tebl/C64-Pi1541-II/gallery/2020-09-29 00.47.54.jpg

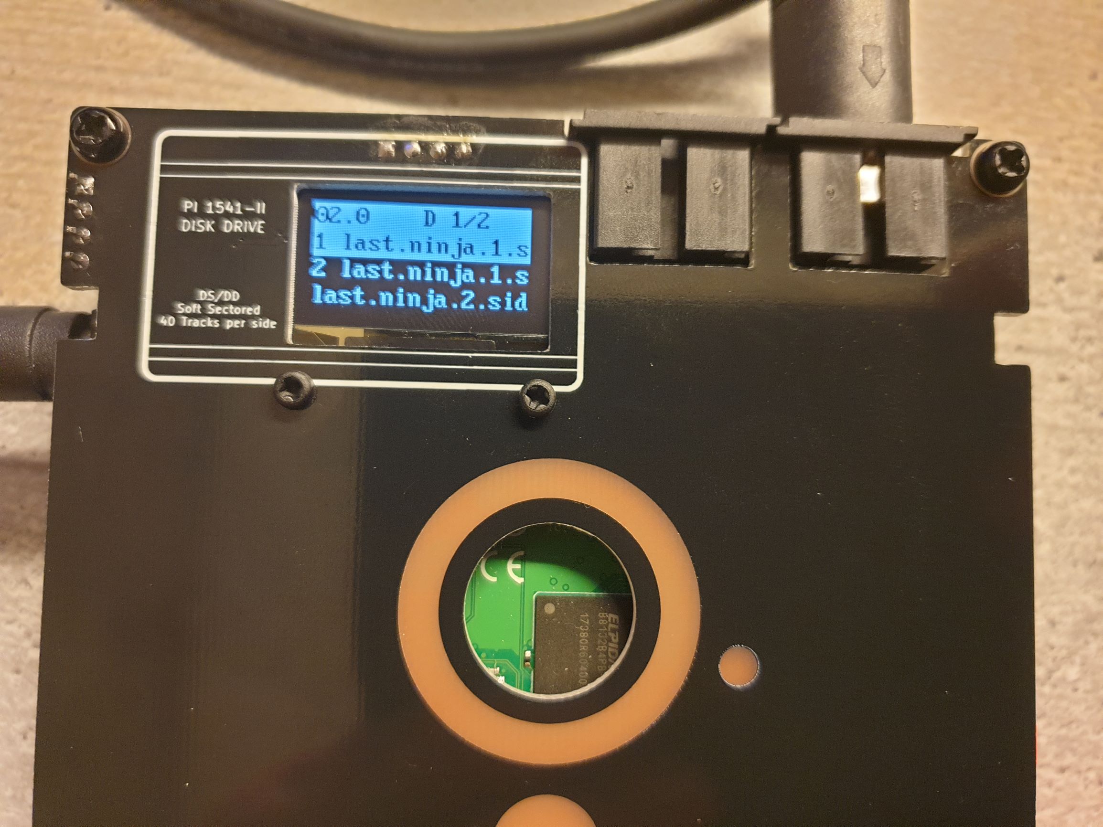
gallery/2020-09-29 00.47.54.jpg
