tebl/C64-Pi1541-II/gallery/2020-11-05 23.57.20.jpg

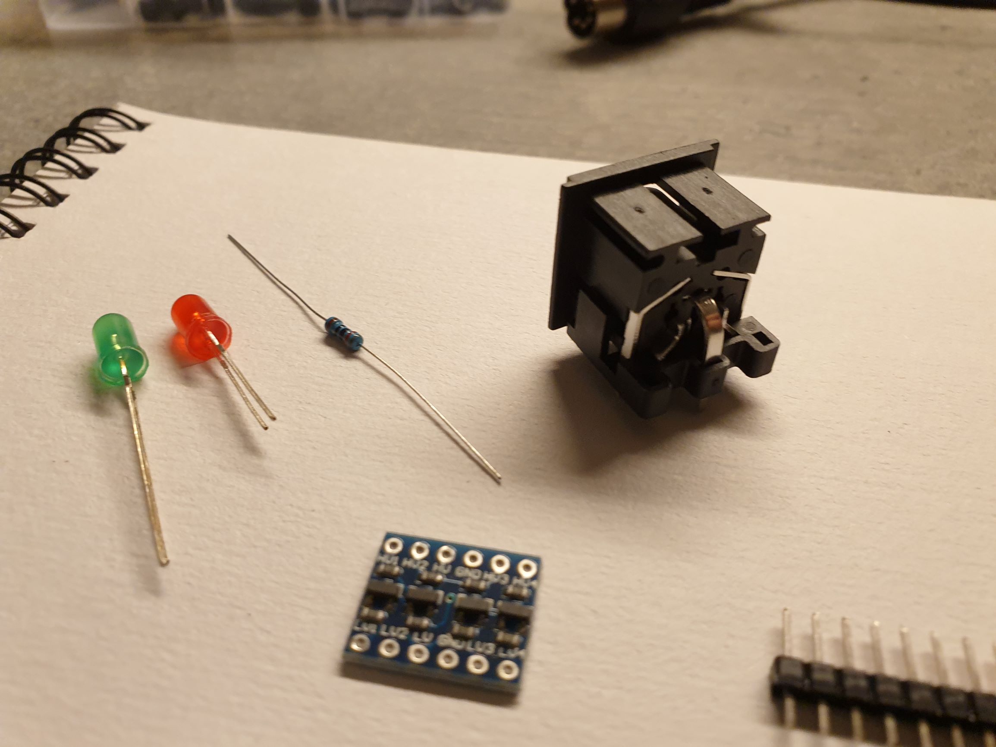
gallery/2020-11-05 23.57.20.jpg
